GustavAbrahamsson/Mechatronic-Hand/CAD/Hand_02-06-22/Fingers 2.7/Index/Proximal phalanx.stl

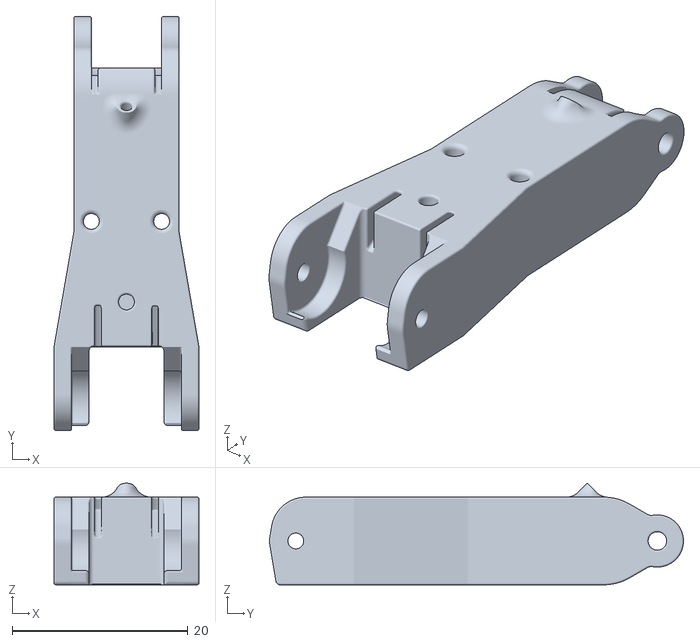
[picture p20: CAD file, 2022-04-28]
CAD/Hand_02-06-22/Fingers 2.7/Index/Proximal phalanx.stl
16.5 x 47.2 x 11.6
