GustavAbrahamsson/Mechatronic-Hand/CAD/Hand_02-06-22/Fingers 2.7/Molds for finger tips/Finger mold/top.stl

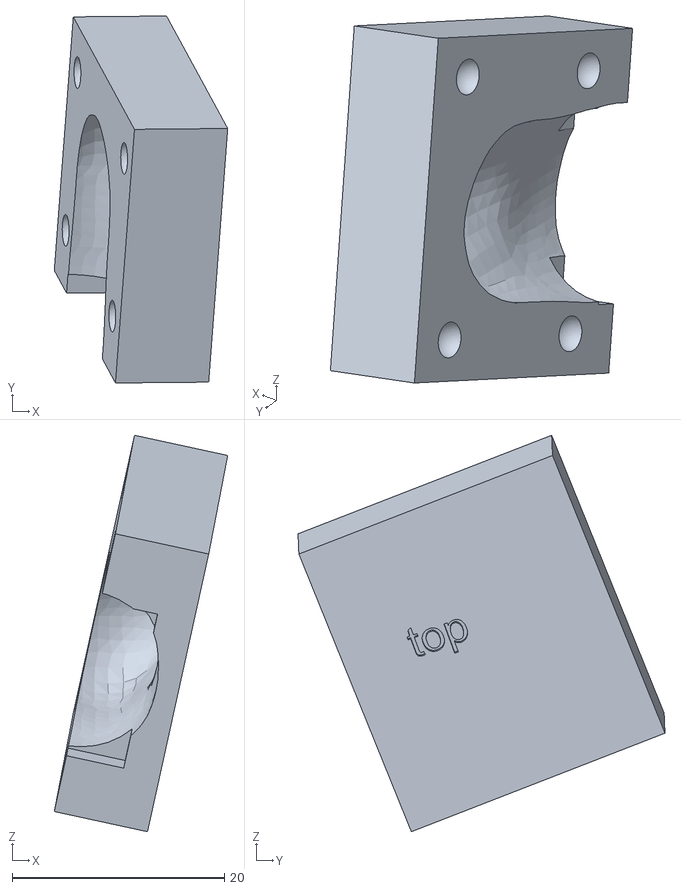
[picture p21: CAD file, 2022-06-02]
CAD/Hand_02-06-22/Fingers 2.7/Molds for finger tips/Finger mold/top.stl
16.4 x 34.6 x 37.4
