GustavAbrahamsson/Mechatronic-Hand/CAD/Hand_02-06-22/Fingers 2.7/Molds for finger tips/Thumb mold/Bottom.stl

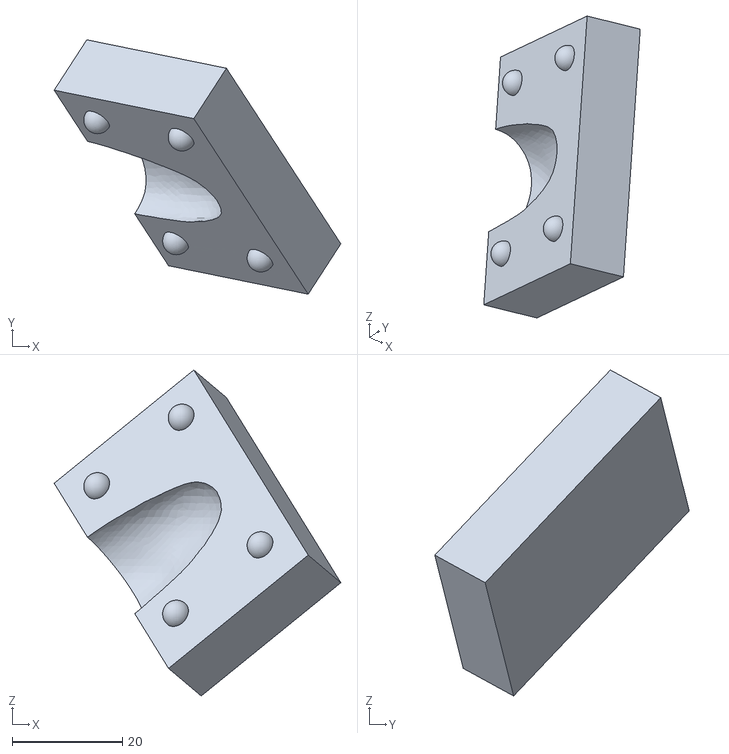
[picture p22: CAD file, 2022-06-02]
CAD/Hand_02-06-22/Fingers 2.7/Molds for finger tips/Thumb mold/Bottom.stl
52.1 x 46.2 x 59.2
