GustavAbrahamsson/Mechatronic-Hand/CAD/Hand_02-06-22/Lower arm 1.0/Connector.stl

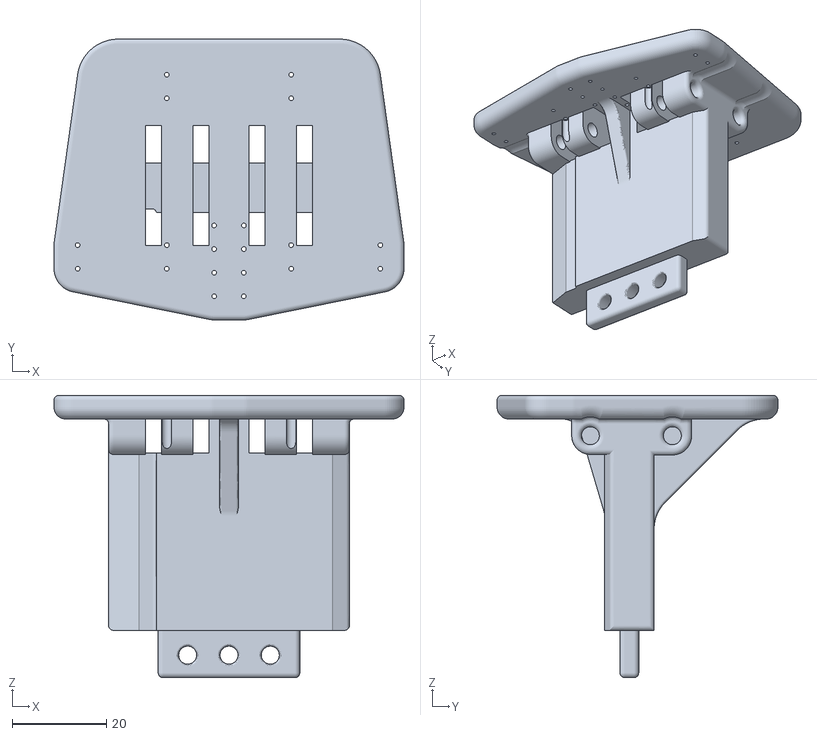
[picture p23: CAD file, 2022-06-02]
CAD/Hand_02-06-22/Lower arm 1.0/Connector.stl
74.1 x 59.5 x 59.8
