GustavAbrahamsson/Mechatronic-Hand/CAD/Hand_02-06-22/Thumb 1.5/CMCpart.stl

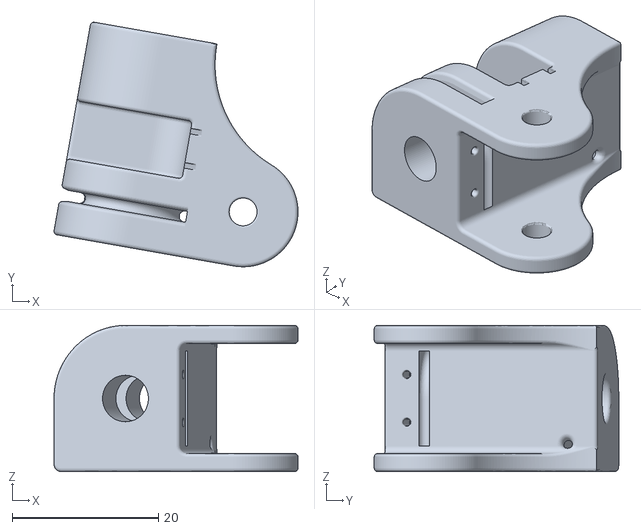
[picture p24: CAD file, 2022-04-28]
CAD/Hand_02-06-22/Thumb 1.5/CMCpart.stl
33.3 x 33.4 x 20.0
