GustavAbrahamsson/Mechatronic-Hand/CAD/Hand_02-06-22/Wrist 1.1/Wrist.stl

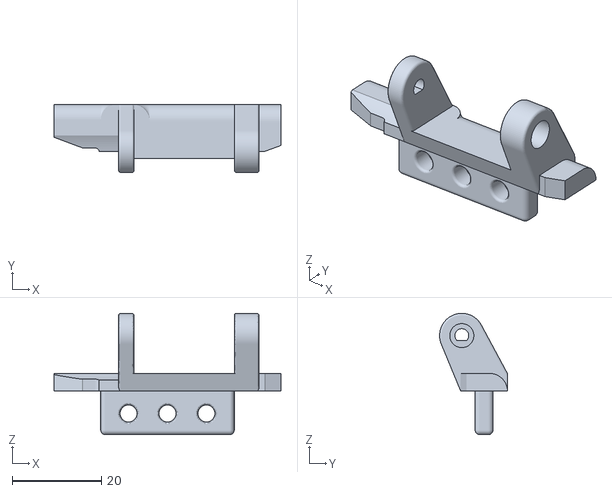
[picture p25: CAD file, 2022-06-02]
CAD/Hand_02-06-22/Wrist 1.1/Wrist.stl
51.0 x 15.2 x 27.2
