GustavAbrahamsson/Mechatronic-Hand/CAD/Hand_02-06-22/Casing/IndexProxFront.stl

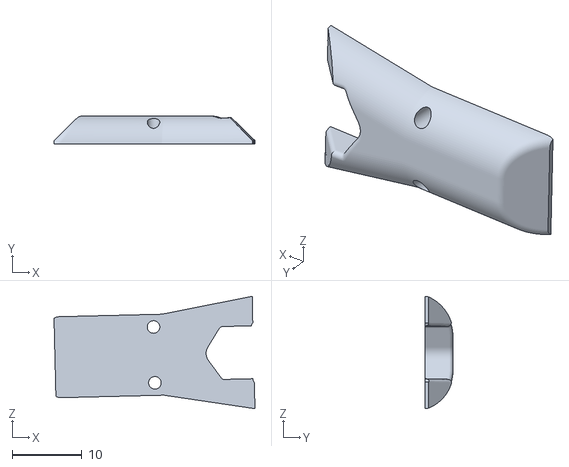
[picture p26: CAD file, 2022-06-02]
CAD/Hand_02-06-22/Casing/IndexProxFront.stl
28.8 x 4.00 x 16.1
