GustavAbrahamsson/Mechatronic-Hand/CAD/Hand_02-06-22/Fingers 2.7/Little/Proximal phalanx.stl

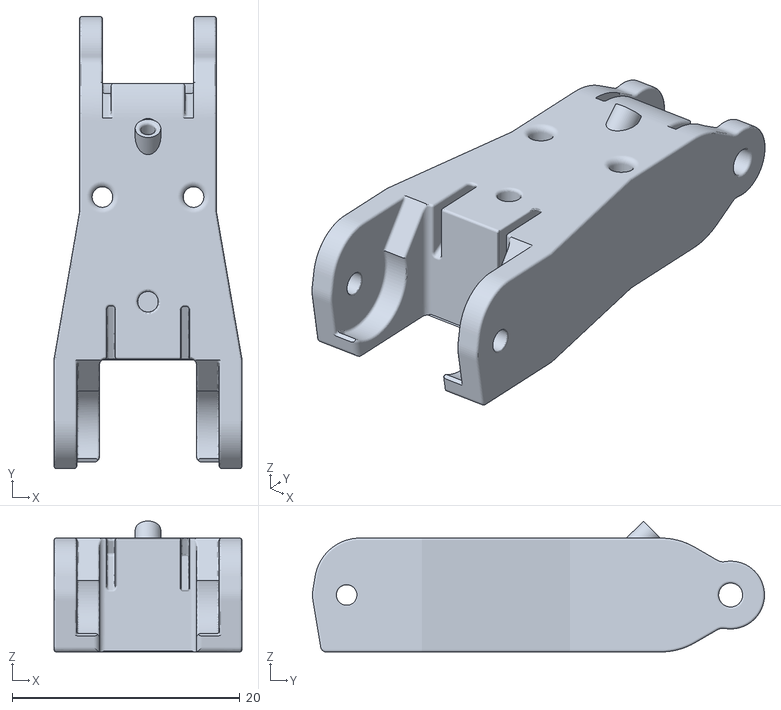
[picture p27: CAD file, 2022-04-28]
CAD/Hand_02-06-22/Fingers 2.7/Little/Proximal phalanx.stl
16.5 x 39.7 x 11.5
