GustavAbrahamsson/Mechatronic-Hand/CAD/Hand_02-06-22/Fingers 2.7/Ring/Proximal phalanx.stl

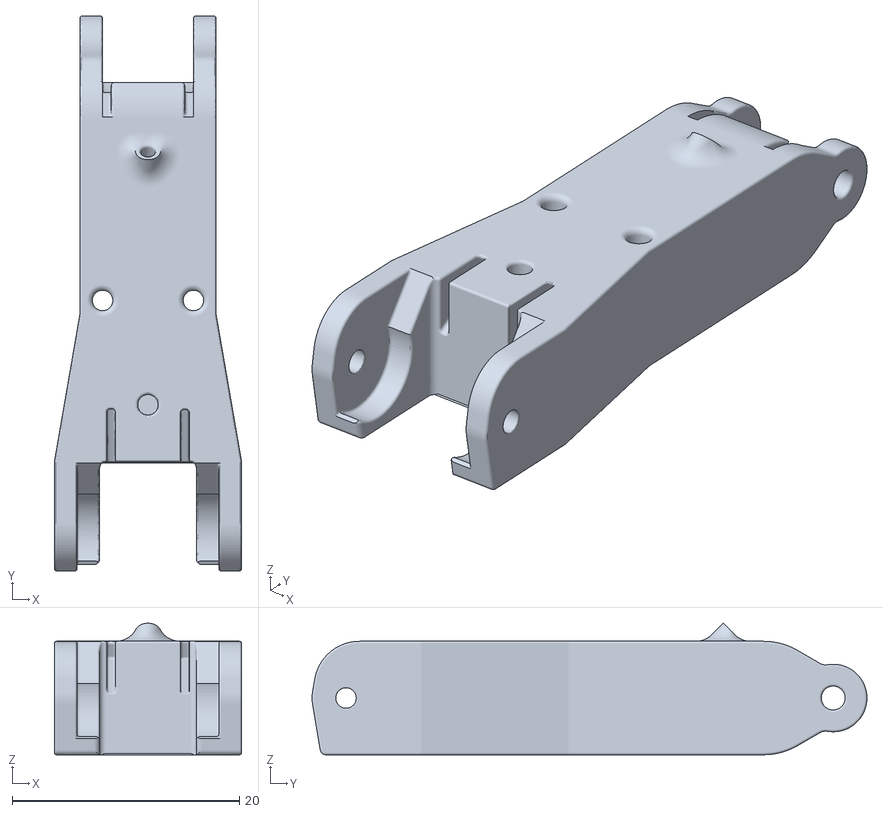
[picture p29: CAD file, 2022-04-28]
CAD/Hand_02-06-22/Fingers 2.7/Ring/Proximal phalanx.stl
16.5 x 48.9 x 11.6
