GustavAbrahamsson/Mechatronic-Hand/CAD/Hand_02-06-22/Lower arm 1.0/8.8mmDistans.stl

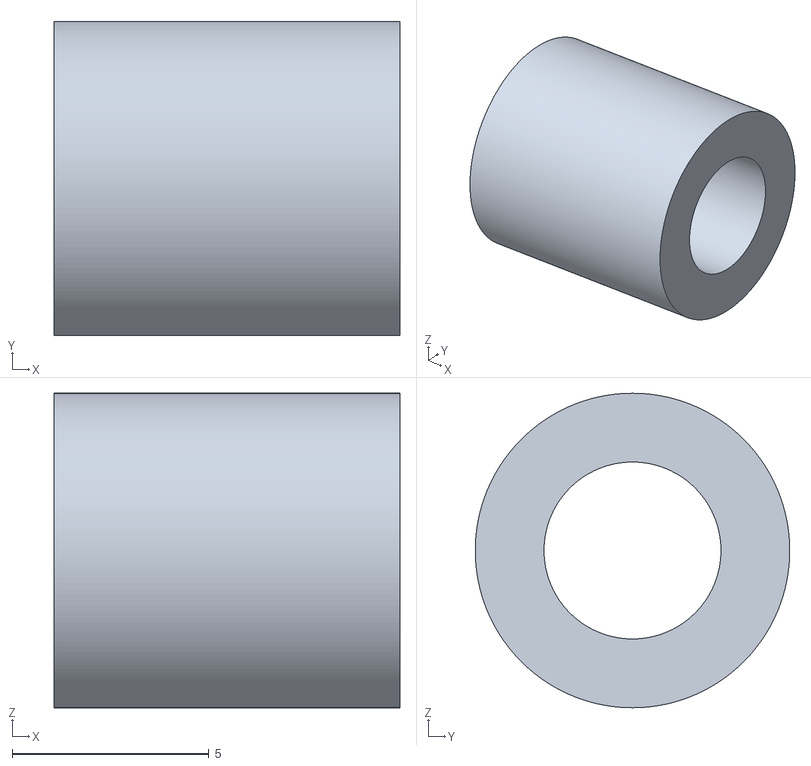
[picture p30: CAD file, 2022-06-02]
CAD/Hand_02-06-22/Lower arm 1.0/8.8mmDistans.stl
8.80 x 8.00 x 8.00
