GustavAbrahamsson/Mechatronic-Hand/CAD/Hand_02-06-22/Thumb 1.5/Intermediatethumb_new v5.stl

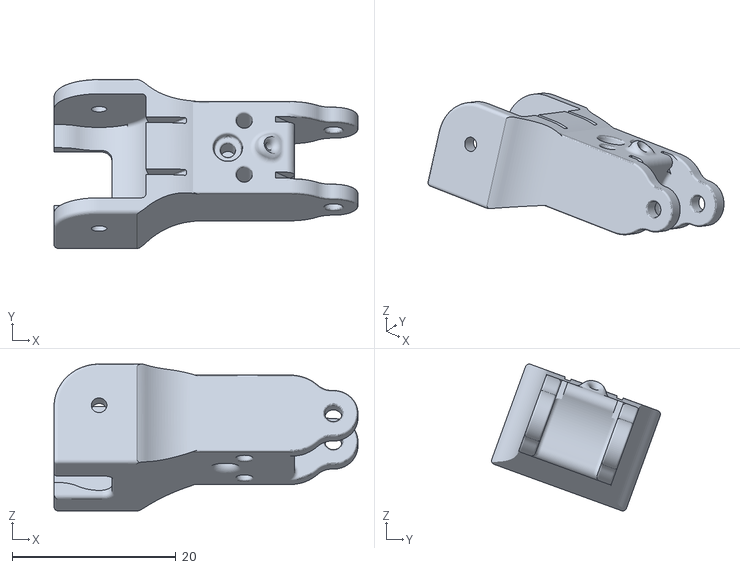
[picture p31: CAD file, 2022-04-28]
CAD/Hand_02-06-22/Thumb 1.5/Intermediatethumb_new v5.stl
37.1 x 20.6 x 17.9
