GustavAbrahamsson/Mechatronic-Hand/CAD/Hand_02-06-22/Wrist 1.1/WristPart.stl

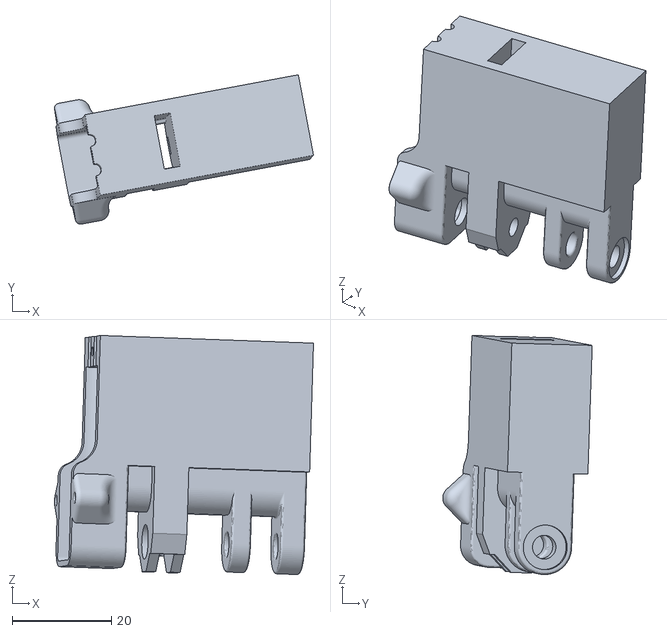
[picture p32: CAD file, 2022-06-02]
CAD/Hand_02-06-22/Wrist 1.1/WristPart.stl
52.2 x 30.1 x 48.2
