GustavAbrahamsson/Mechatronic-Hand/CAD/Hand_02-06-22/Casing/SoftDistal.stl

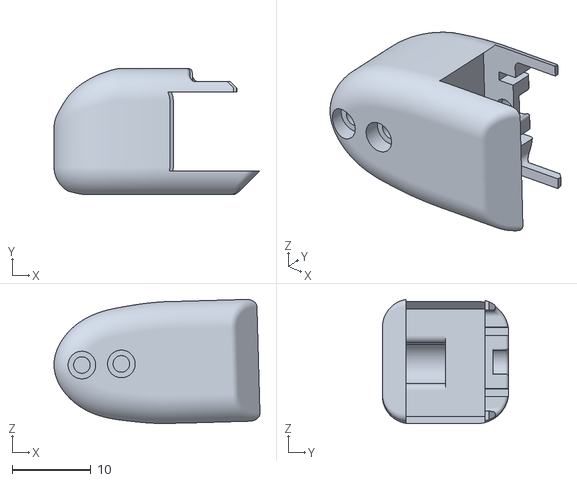
[picture p33: CAD file, 2022-06-02]
CAD/Hand_02-06-22/Casing/SoftDistal.stl
26.1 x 16.0 x 15.7
