GustavAbrahamsson/Mechatronic-Hand/CAD/Hand_02-06-22/Fingers 2.7/Little/Intermediate phalanx.stl

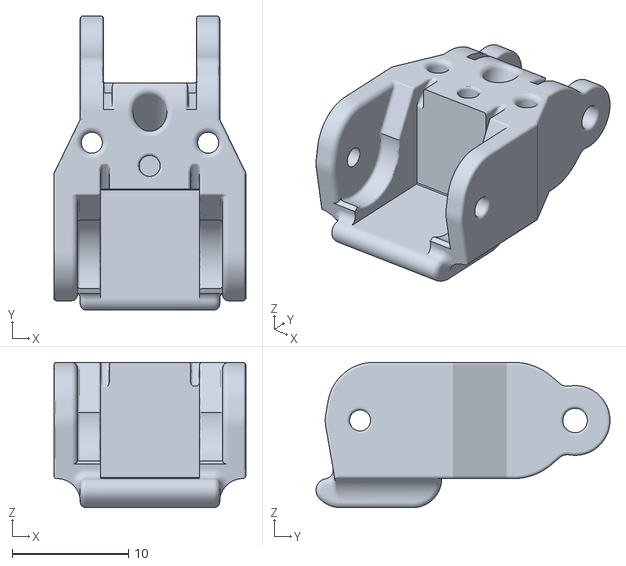
[picture p34: CAD file, 2022-04-28]
CAD/Hand_02-06-22/Fingers 2.7/Little/Intermediate phalanx.stl
16.5 x 25.3 x 12.5
