GustavAbrahamsson/Mechatronic-Hand/CAD/Hand_02-06-22/Fingers 2.7/Ring/Intermediate phalanx.stl

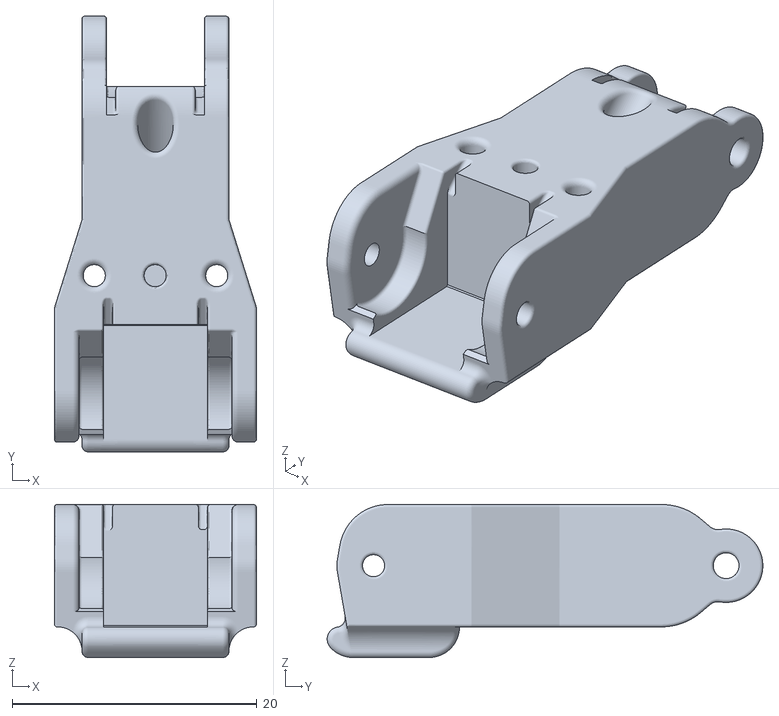
[picture p35: CAD file, 2022-04-28]
CAD/Hand_02-06-22/Fingers 2.7/Ring/Intermediate phalanx.stl
16.5 x 35.6 x 12.5
