GustavAbrahamsson/Mechatronic-Hand/CAD/Hand_02-06-22/Lower arm 1.0/sidePlate1.0.dxf

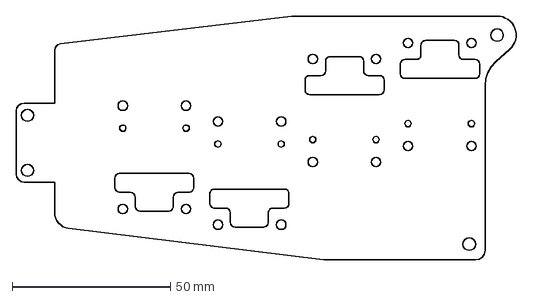
[picture p36: CAD file, 2022-06-02]
CAD/Hand_02-06-22/Lower arm 1.0/sidePlate1.0.dxf
158.4 x 77.0 mm
