GustavAbrahamsson/Mechatronic-Hand/CAD/Hand_02-06-22/Casing/Short distal.stl

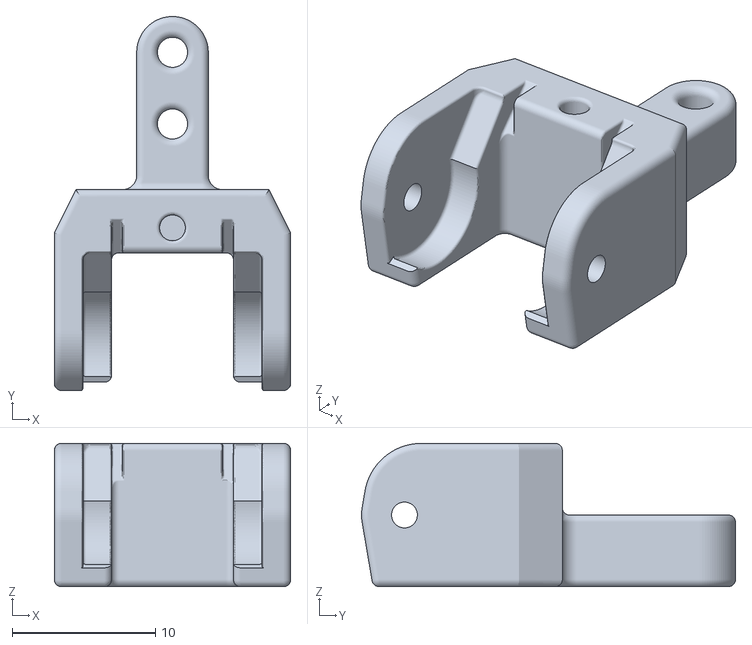
[picture p37: CAD file, 2022-06-02]
CAD/Hand_02-06-22/Casing/Short distal.stl
16.5 x 26.1 x 10.0
