GustavAbrahamsson/Mechatronic-Hand/CAD/Hand_02-06-22/Casing/IndexInterFront.stl

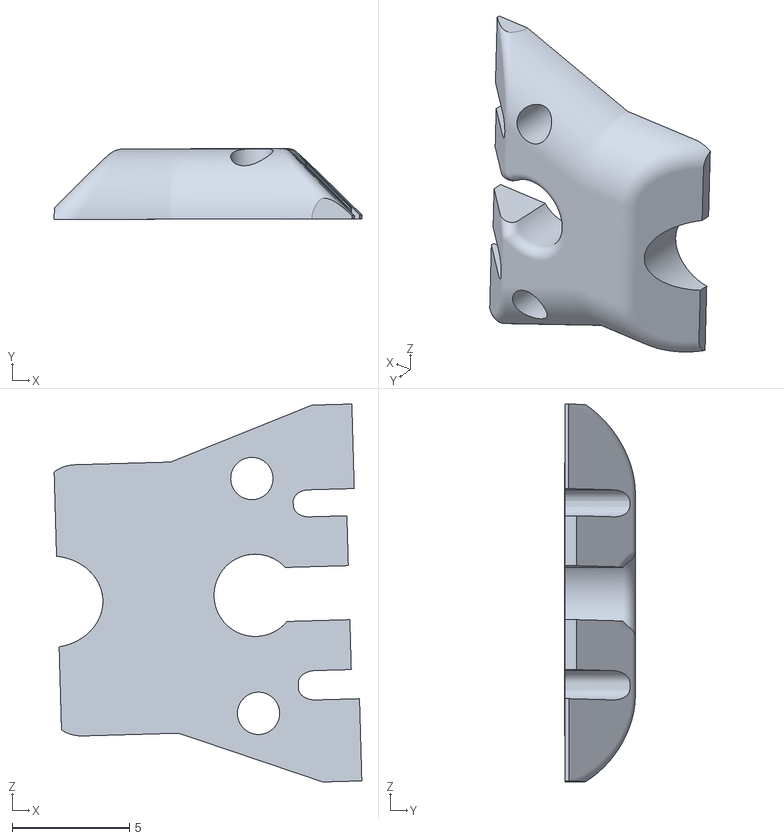
[picture p38: CAD file, 2022-06-02]
CAD/Hand_02-06-22/Casing/IndexInterFront.stl
13.1 x 3.01 x 16.1
