GustavAbrahamsson/Mechatronic-Hand/CAD/Hand_02-06-22/Lower arm 1.0/7mmDistans.stl

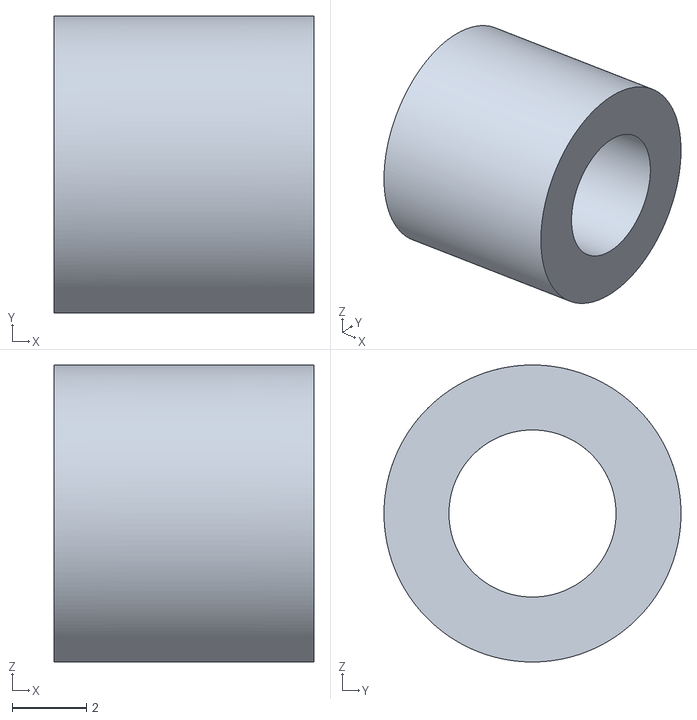
[picture p39: CAD file, 2022-06-02]
CAD/Hand_02-06-22/Lower arm 1.0/7mmDistans.stl
7.00 x 8.00 x 8.00
