GustavAbrahamsson/Mechatronic-Hand/CAD/Hand_02-06-22/Lower arm 1.0/3DprintedBase.stl

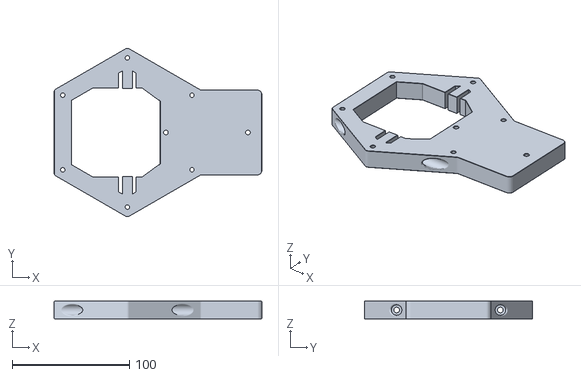
[picture p40: CAD file, 2022-06-02]
CAD/Hand_02-06-22/Lower arm 1.0/3DprintedBase.stl
177.5 x 143.7 x 15.0
