GustavAbrahamsson/Mechatronic-Hand/Results/Cutkosky2.PNG

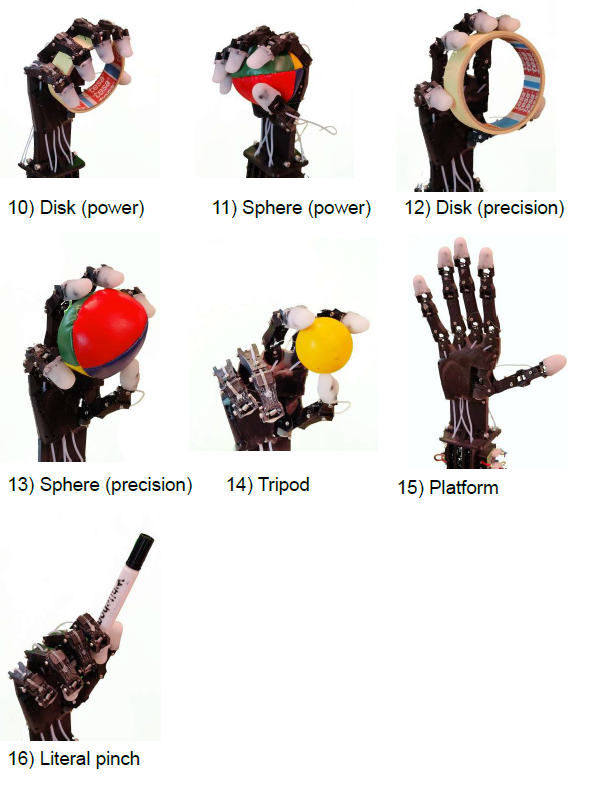
Results/Cutkosky2.PNG
