GustavAbrahamsson/Mechatronic-Hand/Results/SignlanguageAlphabet2.PNG

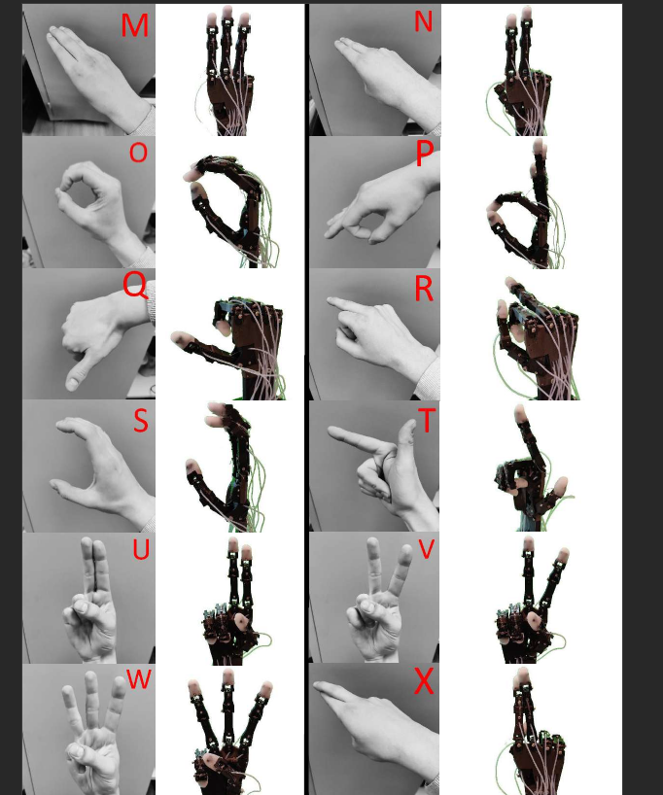
Results/SignlanguageAlphabet2.PNG
