GustavAbrahamsson/Mechatronic-Hand/ESPHandControl/src/angles.h

// A	0	0	101	0	75	15	12	68	15	20	68	15	20	67	5	20
// B	0	0	0	0	90	90	0	90	90	0	90	90	0	90	90	0
// C	20	20	48	0	28	30	0	28	30	0	28	30	0	28	30	0
// D	0	90	90	0	0	0	0	0	0	0	0	0	0	0	0	0
// E	90	90	82	33	90	47	0	90	51	0	90	85	0	90	90	0
// F	0	0	80	38	30	90	0	0	0	0	0	0	0	0	0	0
// G	0	30	60	0	90	90	0	90	90	0	90	90	0	90	90	0
// H	10	20	38	0	45	40	0	10	0	0	10	0	0	10	0	0
// I	0	30	60	0	90	90	0	90	90	0	90	90	0	0	0	0
// J	0	0	0	90	0	0	0	0	0	0	0	0	0	0	0	0
// K	0	15	80	20	0	0	0	45	0	0	90	90	0	90	90	0
// L	0	30	60	0	0	0	0	90	90	0	90	90	0	90	90	0
// M	0	90	90	0	0	0	0	0	0	0	0	0	0	0	0	0
// N	0	30	60	0	0	0	0	0	0	0	90	90	0	90	90	0
// O	10	20	43	0	45	40	0	45	40	0	45	40	0	45	40	0
// P	10	20	42	0	45	45	0	10	0	0	10	0	0	10	0	0
// Q	0	0	0	0	90	90	0	90	90	0	90	90	0	90	90	0
// R	0	30	60	0	90	90	0	90	0	0	90	90	0	90	90	0
// S	20	20	48	0	28	30	0	28	30	0	28	30	0	28	30	0
// T	0	0	0	0	30	0	0	90	90	0	90	90	0	90	90	0
// U	0	30	60	0	0	0	0	0	0	0	90	90	0	90	90	0
// V	0	30	60	0	0	0	30	0	0	−10	90	90	0	90	90	0
// W	0	30	60	0	0	0	30	0	0	0	0	0	−30	90	90	−10
// X	0	30	60	0	15	0	0	0	0	10	90	90	0	90	90	0
// Y	0   0   0   0   0   0   0   0   0   0   0   0   0   0   0   0 															
// Z	0	30	60	0	0	0	0	90	90	0	90	90	0	90	90	0




int a[16] = {0,   0, 90,  0, 60, 30,  0, 60, 30, 20, 60, 30, 20, 75,  30, 20};
int b[16] = {0,   0,  0,  0, 90, 90,  0, 90, 90, 0,  90, 90,  0, 90, 90,  0};
int c[16] = {15, 20, 60,  0,  0, 45,  0,  0, 45, 0,   0, 45,-15,  0, 45, -15};
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
int precision_sphere[16] = {0, 20, 80, 0, 20, 45, 0, 10, 45, 0, 20, 45, 0, 40, 50, 30};//M
int tripod[16] = {10, 20, 60, 0, 55, 50, 30, 45, 40, 0, 90, 90, 0, 90, 90, 0};//N
int platform_push[16] = {0, 0, 0, 0, 0, 0, 0, 0, 0, 0, 0, 0, 0, 0, 0, 0};//O
int lateral_pinch[16] = {0, 0, 80, 38, 40, 90, 0, 50, 90, 0, 60, 90, 0, 70, 90, 0};//P



//array containg all letters
int * letters[] = {a, b, c, d, e, f, g, h, i, j, k, l, m, n, o, p, q, r, s, t, u, v, w, x, y, z, fu, yeah};

//array containing all grips
int * grips[] = {large_diameter, medium_diameter, medium_wrap, abducted_thumb, light_tool, thumb_4_finger, thumb_3_finger, thumb_2_finger, thumb_index, power_disc, power_sphere, precision_disc, precision_sphere, tripod, platform_push, lateral_pinch};
